5881/RDA5807_RDS/man/2025-08-19-20:02:30-DIANA.png

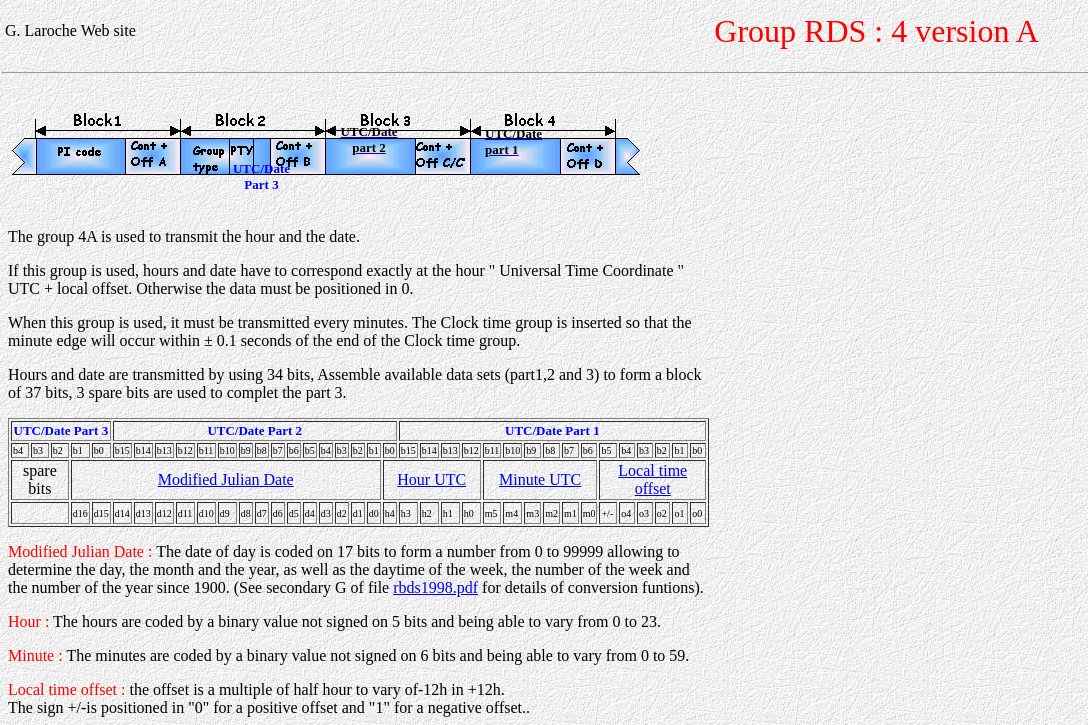
man/2025-08-19-20:02:30-DIANA.png
