5881/RDA5807_RDS/pics/IMG_20250820_172304.jpg

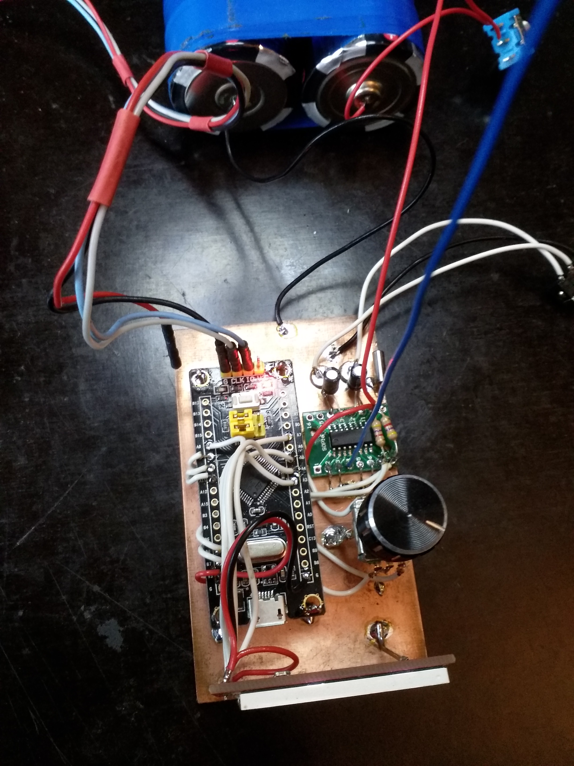
pics/IMG_20250820_172304.jpg
