5881/RDA5807_RDS/pics/IMG_20250820_174653.jpg

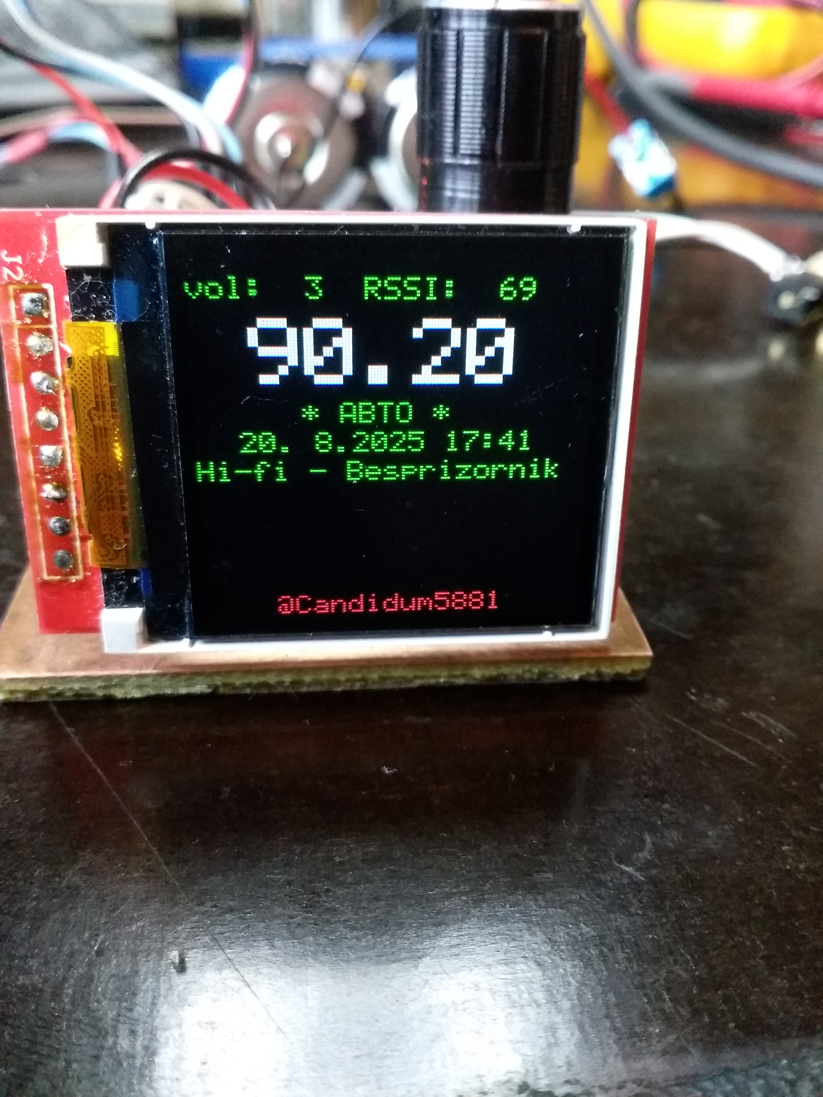
pics/IMG_20250820_174653.jpg
