5881/RDA5807_RDS/pics/IMG_20250830_223725.jpg

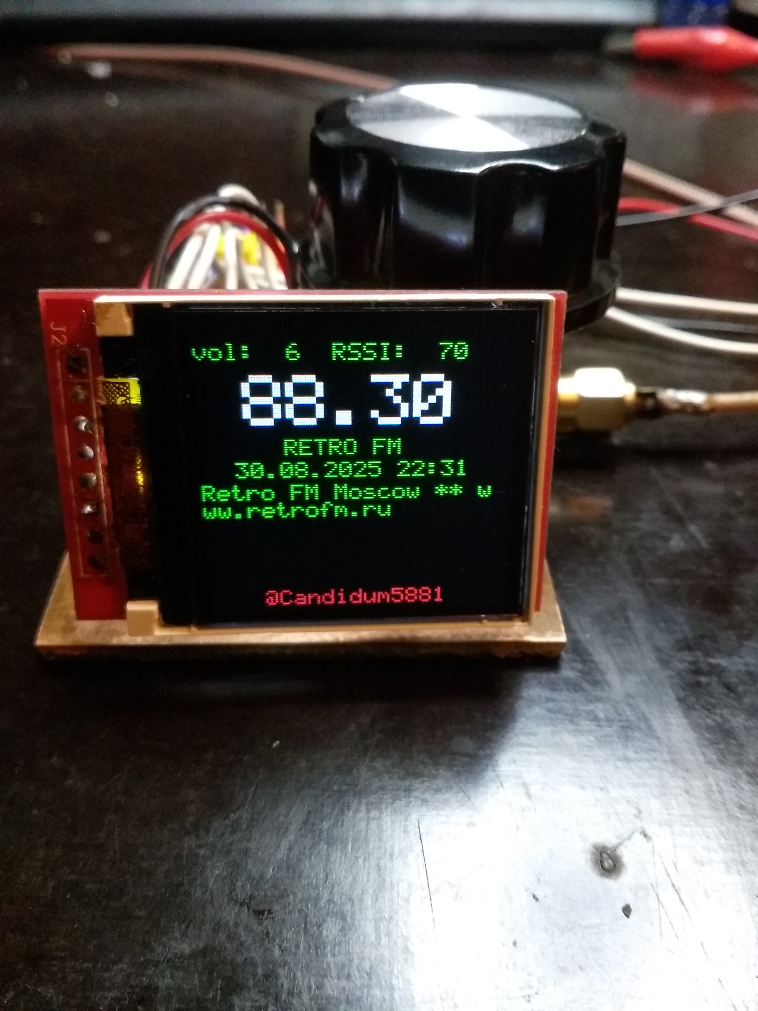
pics/IMG_20250830_223725.jpg
