5881/RDA5807_RDS/pics/IMG_20250830_230445.jpg

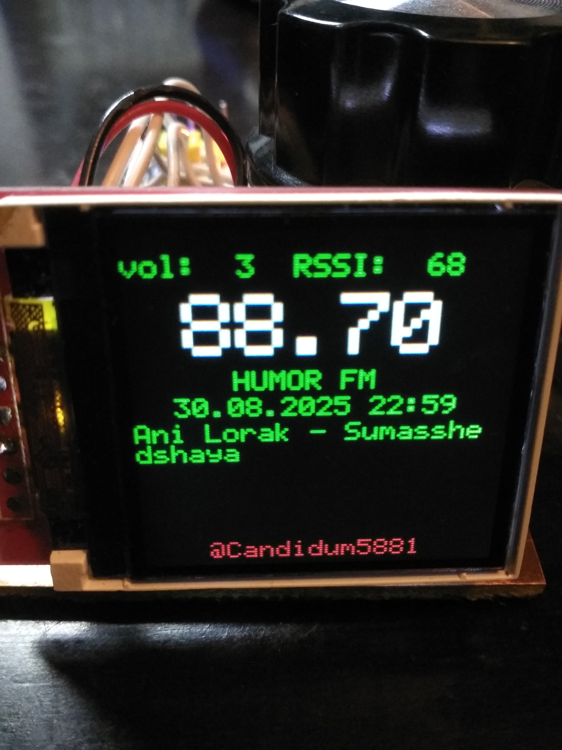
pics/IMG_20250830_230445.jpg
