5881/RDA5807_RDS/schematic/rda5807fp.kicad_sch

## KiCad design schematic/rda5807fp.kicad_sch (2025-08-20)

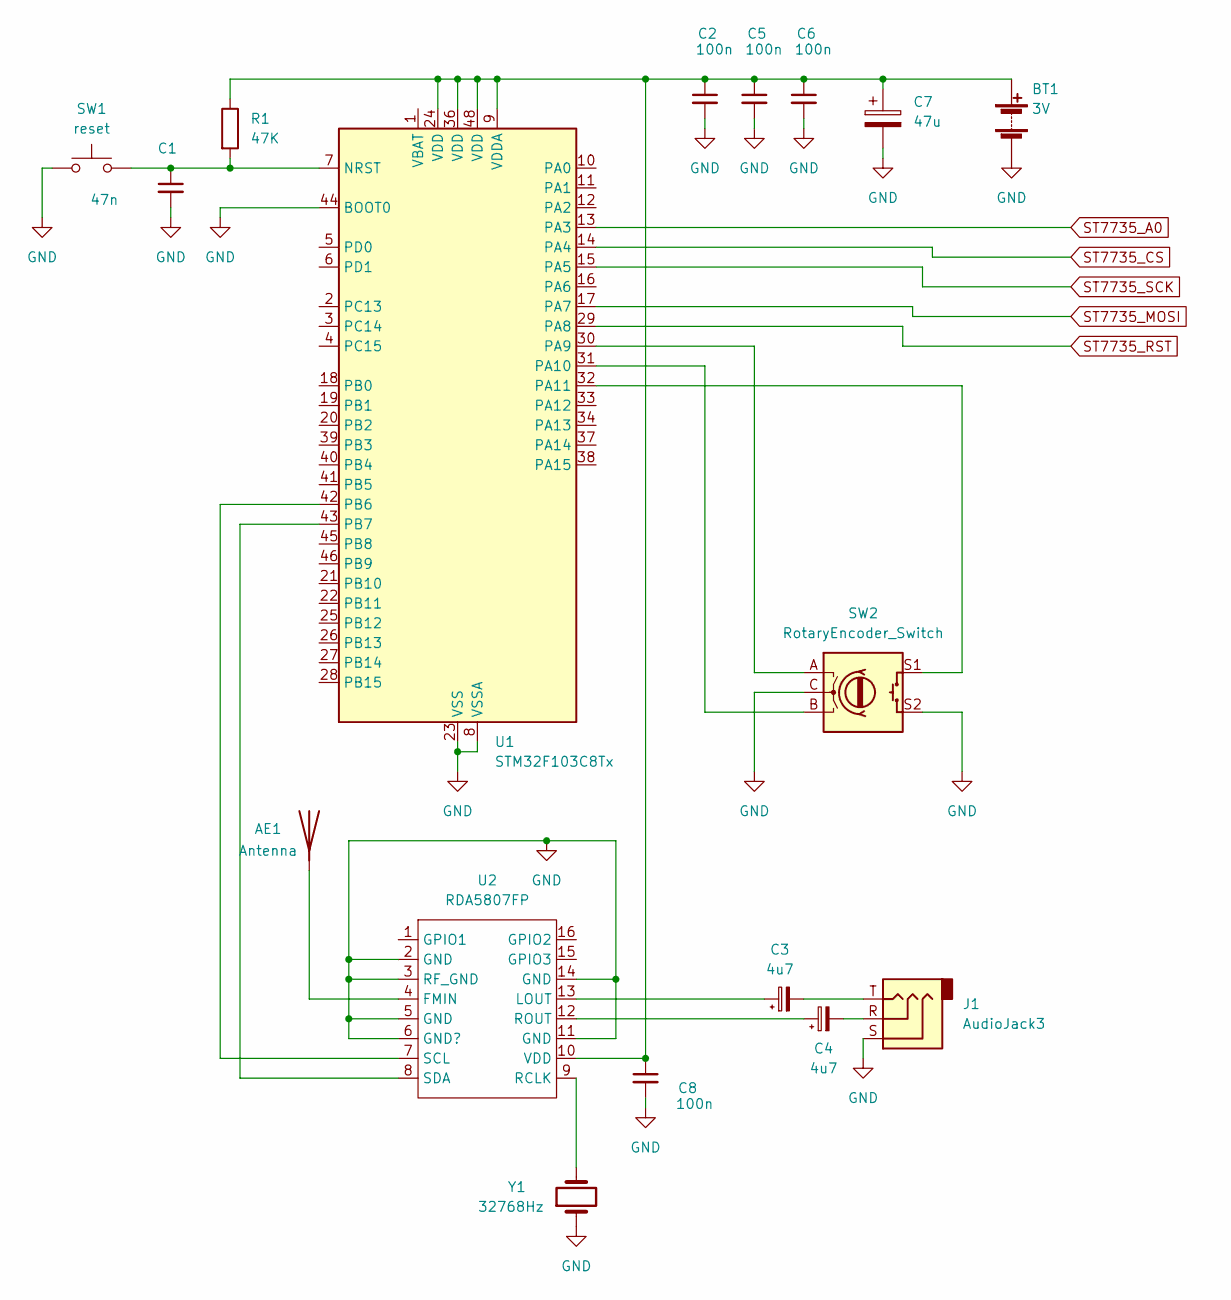
[picture p19: schematic rda5807fp.kicad_sch]

Parts:
AE1: Antenna
BT1: 3V
C1: 47n
C2, C5, C6, C8: 100n
C3, C4: 4u7
C7: 47u
J1: AudioJack3
R1: 47K
SW1: reset
SW2: RotaryEncoder_Switch
U1: STM32F103C8Tx; LQFP-48_7x7mm_P0.5mm
U2: RDA5807FP
Y1: 32768Hz

Connections:
GND: BT1.2 (-), C1.2, C2.2, C5.2, C6.2, C7.2, C8.2, J1.S, SW1.1, SW2.C, SW2.S2, U1.8 (VSSA), U1.23 (VSS), U1.35 (VSS), U1.44 (BOOT0), U1.47 (VSS), U2.2 (GND), U2.3 (RF_GND), U2.5 (GND), U2.6 (GND?), U2.11 (GND), U2.14 (GND), Y1.1
unnamed: AE1.1, U2.4 (FMIN)
unnamed: BT1.1 (+), C2.1, C5.1, C6.1, C7.1, C8.1, R1.1, U1.9 (VDDA), U1.24 (VDD), U1.36 (VDD), U1.48 (VDD), U2.10 (VDD)
unnamed: C1.1, R1.2, SW1.2, U1.7 (NRST)
unnamed: C3.1, U2.13 (LOUT)
unnamed: C3.2, J1.T
unnamed: C4.1, U2.12 (ROUT)
unnamed: C4.2, J1.R
unnamed: SW2.A, U1.30 (PA9)
unnamed: SW2.B, U1.31 (PA10)
unnamed: SW2.S1, U1.32 (PA11)
unnamed: U1.42 (PB6), U2.7 (SCL)
unnamed: U1.43 (PB7), U2.8 (SDA)
unnamed: U2.9 (RCLK), Y1.2
ST7735_A0: U1.13 (PA3)
ST7735_CS: U1.14 (PA4)
ST7735_MOSI: U1.17 (PA7)
ST7735_RST: U1.29 (PA8)
ST7735_SCK: U1.15 (PA5)
