5881/RDA5807_RDS/logo2.h

/* GIMP RGB C-Source image dump (logo2.c) */

static const uint8_t LOGO2[128 * 128 * 2] =(
  "\345\220\006\221\006\221\006\221\006\211\006\211\345\220\327\325\\\347;\357\363\314"
  "\070\346\231\346X\336\331\346\271\346\271\346\271\346\271\346\271\346\271"
  "\346\271\346\331\346\271\346\271\346\271\346\271\346\271\346\271\346\271"
  "\346\271\346\271\346\271\346\271\346\271\346\271\346\271\346\271\346\271"
  "\346\271\346\271\346\271\346\271\346\271\346\230\346\230\346\271\346\271"
  "\346\271\346\271\346W\336\026\326\264\315\224\315s\315\224\315\264\315s\305"
  "\224\315\324\315\062\305\026\326\231\346\271\346\271\346\271\346\271\346\271"
  "\346\271\346\271\346\271\346\271\346\271\346\271\346\271\346\331\356X\346"
  "\020\264*\232\250\231N\243\065\305\367\315\315\252&\221)\232G\241'\231\305"
  "\230\251\252\010\252%\241\005\251\010\272\350\261G\251g\261\354\262)\242\345"
  "\210\006aFiF\231&\221&\201gY%\211\345\240\345p%a\245\020&afyFY\204\210\304\200"
  "\005Q%\251%\221Fq&yFi%y\303\060\243@F\241%\251\005\261\006\211\006\211\006\221&\221"
  "\346\220g\221\351\231\322\304\326\325Q\304\222\304\023\315\224\325\270\346"
  "\331\346\271\346\271\346\271\346\271\346\271\346\271\346\271\346\271\346"
  "\271\346\271\346\271\346\271\346\271\346\271\346\271\346\271\346\271\346"
  "\271\346\271\346\271\346\271\346\271\346\271\346\271\346\271\346\271\346"
  "\271\346\270\346\271\346W\336\066\336W\336\066\336\066\326\026\326\264\315\224"
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
  "\020\202\020A\010A\020A\010A\010\004!Hb\352z\013\203$)\303\030\343\040\344\040\004!%)%"
  ")\004)$)$)\004!\304\210b\070a\000f\061f\061f\061E)(Jm{l{\215\203L{Ls+k\353b\312b\352"
  "b\312b\352b\352b\353b\013c\013k,k\013c\013c\013cLs\256\203\215{lsls\215{\215{"
  ",s\315\213\255\213\315\213\315\213\315\213\315\213\315\203\316\223Q\264\255"
  "\203\255\213\255\213\255\203\255\203\255\203\255\203\255\203\255\203\255"
  "\203\255\203\255\203\255\203\255\203\215\203\215\203\214{\215\203\214{\255"
  "\203\255\203\255\203\215\203\215{l{l{l{LsLs,s,k\013k\013c\013c\353b\353b\312"
  "Z\312Z\252Z\211Z\211R\211R\252Ze\061!\000b\010b\020b\020b\020b\010A\010A\010\243\030"
  "\242\030\000\000ib\220\254P\244P\244iZ!\000!\010a\010b\020b\020A\010A\010A\010A\010b\010"
  "(Zij\252r(Z\303\030\303\030\344\040\004!\004)\005)\004!\004)$)\004)\345`A\030\202\020f\061"
  "F)f)%!\212ZL{+k\013k\013k\353b\312Z\251Z\251Z\251Z\312Z\312b\352b\352b\013c"
  "\013c+kLsm{\316\213\017\224\357\223\357\213\255\203\215{\215{\255\203,s\214"
  "{\315\213\255\213\255\213\255\213\255\213\255\203\357\243Q\274"
);
